Safo001/WorkShops_S2_24/Images/Forces.png

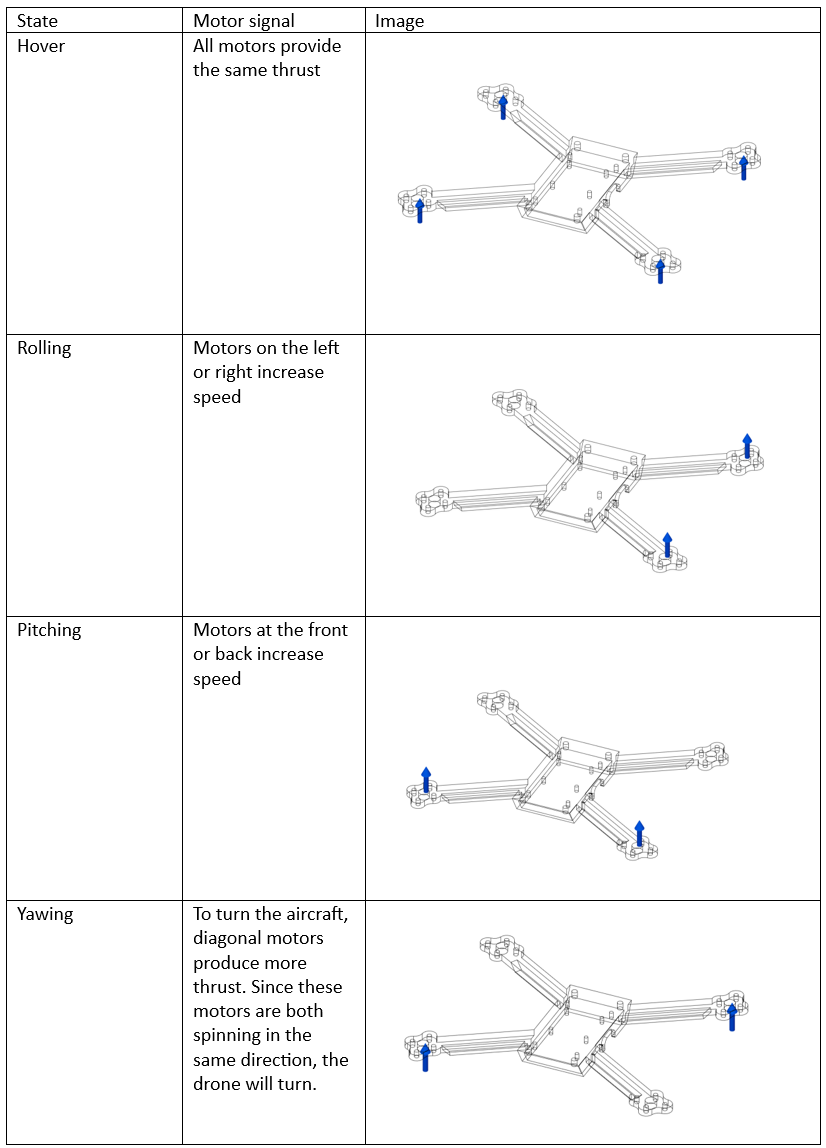
Images/Forces.png
