Safo001/WorkShops_S2_24/Images/Picture4.png

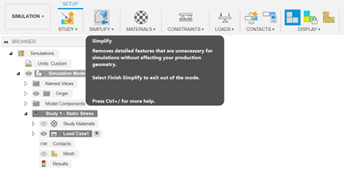
Images/Picture4.png
