Safo001/WorkShops_S2_24/Images/Picture10.png

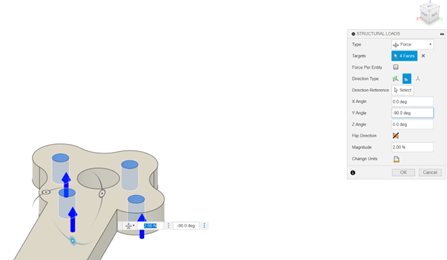
Images/Picture10.png
