Safo001/WorkShops_S2_24/Images/Picture13.png

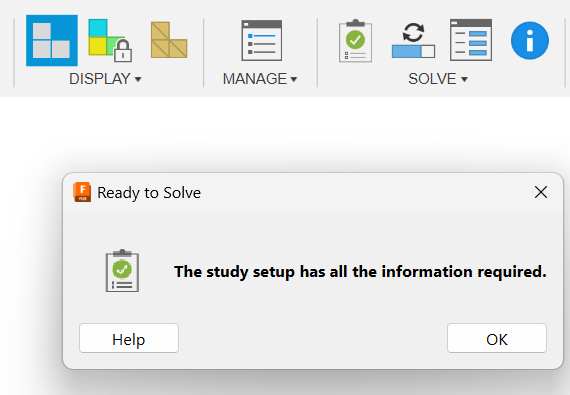
Images/Picture13.png
