Safo001/WorkShops_S2_24/Images/Picture14.png

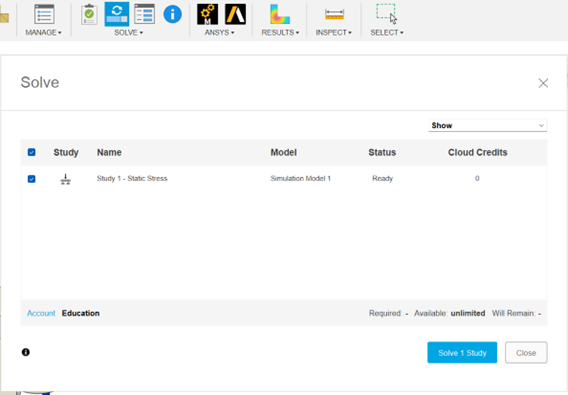
Images/Picture14.png
