Safo001/WorkShops_S2_24/Images/Picture15.png

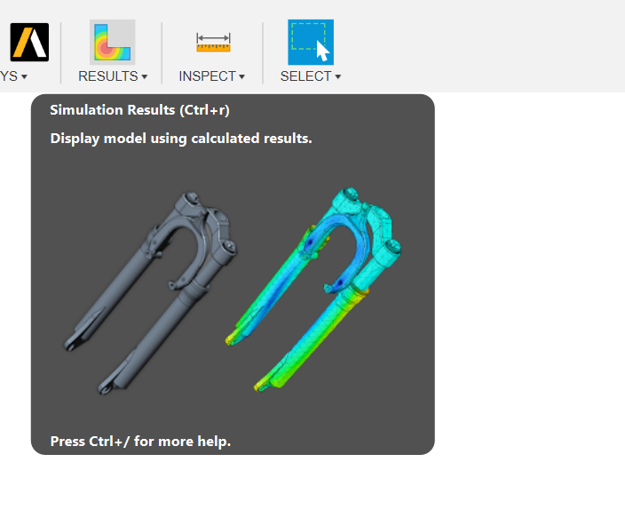
Images/Picture15.png
