Safo001/WorkShops_S2_24/Images/Picture16.png

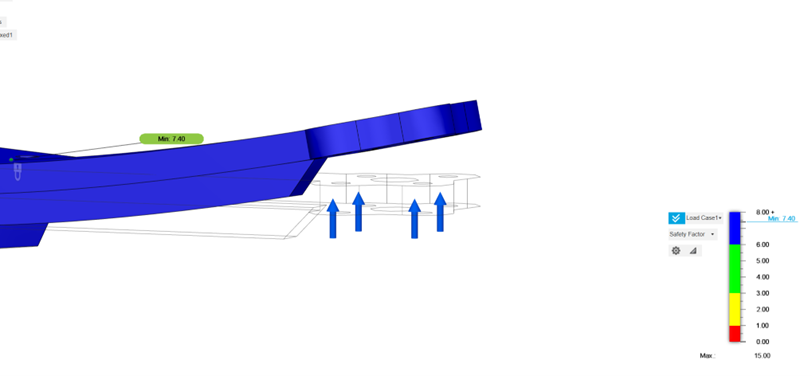
Images/Picture16.png
