Safo001/WorkShops_S2_24/workshop4/Videos/MotorsMounted.jpg

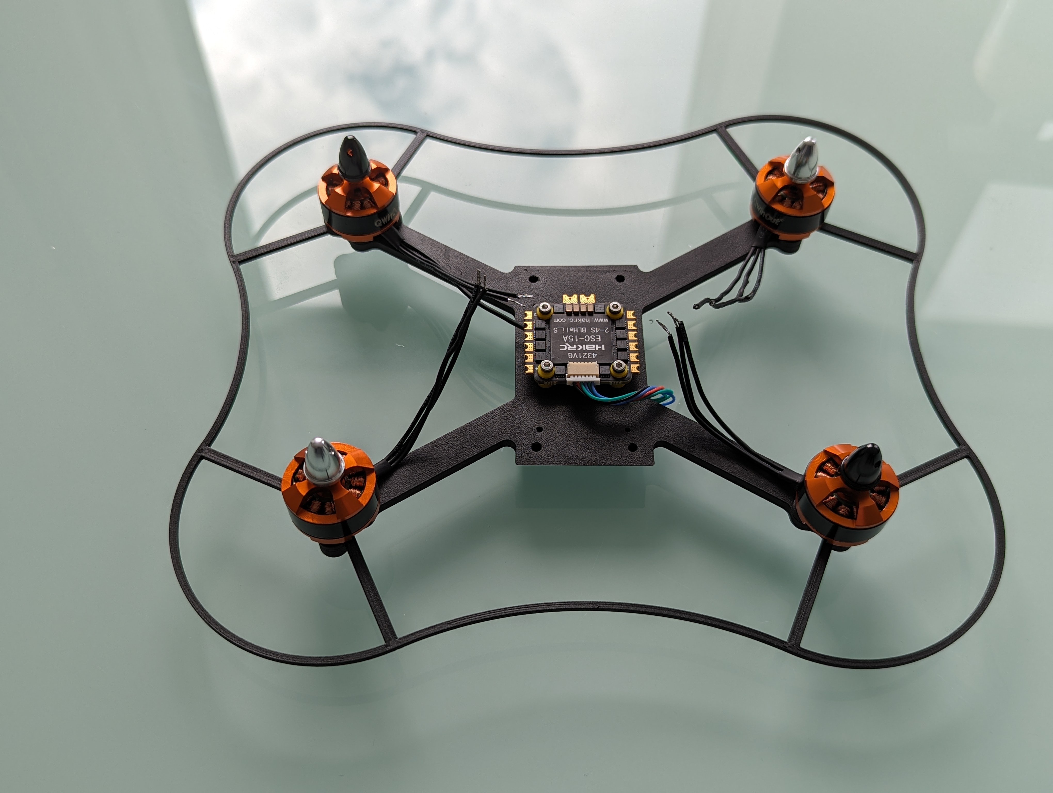
workshop4/Videos/MotorsMounted.jpg
